Bubble2D/Roboarm/3D-Models/3mf-Files/Handteile/Fingerteile/Connector Typ 1/Finger-FingerConnector-Binder_groß.3mf

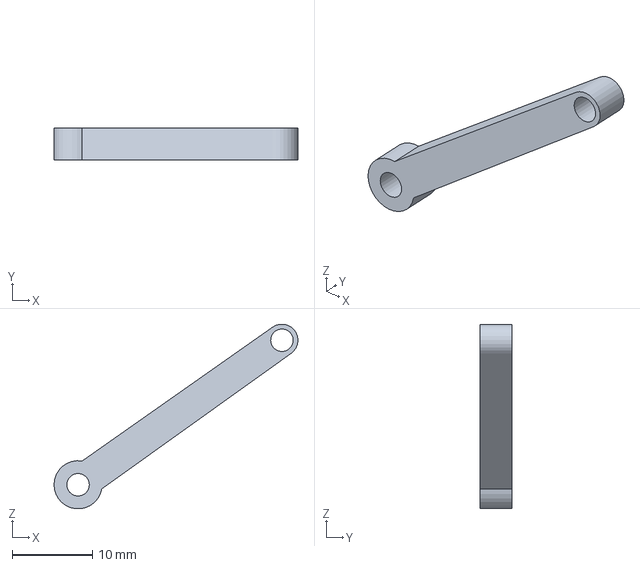
[picture p16: CAD file, 2025-01-12]
3D-Models/3mf-Files/Handteile/Fingerteile/Connector Typ 1/Finger-FingerConnector-Binder_groß.3mf
30.4 x 4.00 x 23.0 mm
