Bubble2D/Roboarm/3D-Models/3mf-Files/Handteile/Fingerteile/Connector Typ 2/Finger-FingerConnector-Binder_klein.3mf

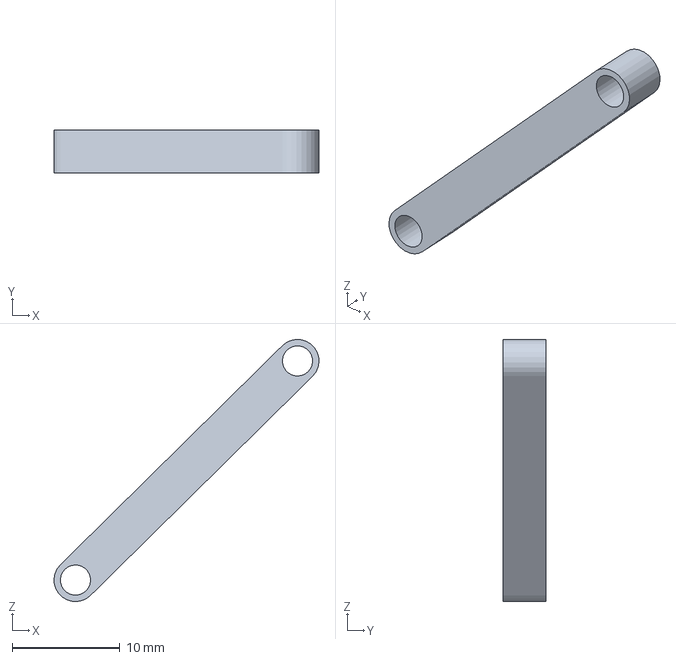
[picture p17: CAD file, 2025-01-12]
3D-Models/3mf-Files/Handteile/Fingerteile/Connector Typ 2/Finger-FingerConnector-Binder_klein.3mf
24.6 x 4.00 x 24.4 mm
