Bubble2D/Roboarm/3D-Models/3mf-Files/Handteile/Fingerteile/Finger-komplett.3mf

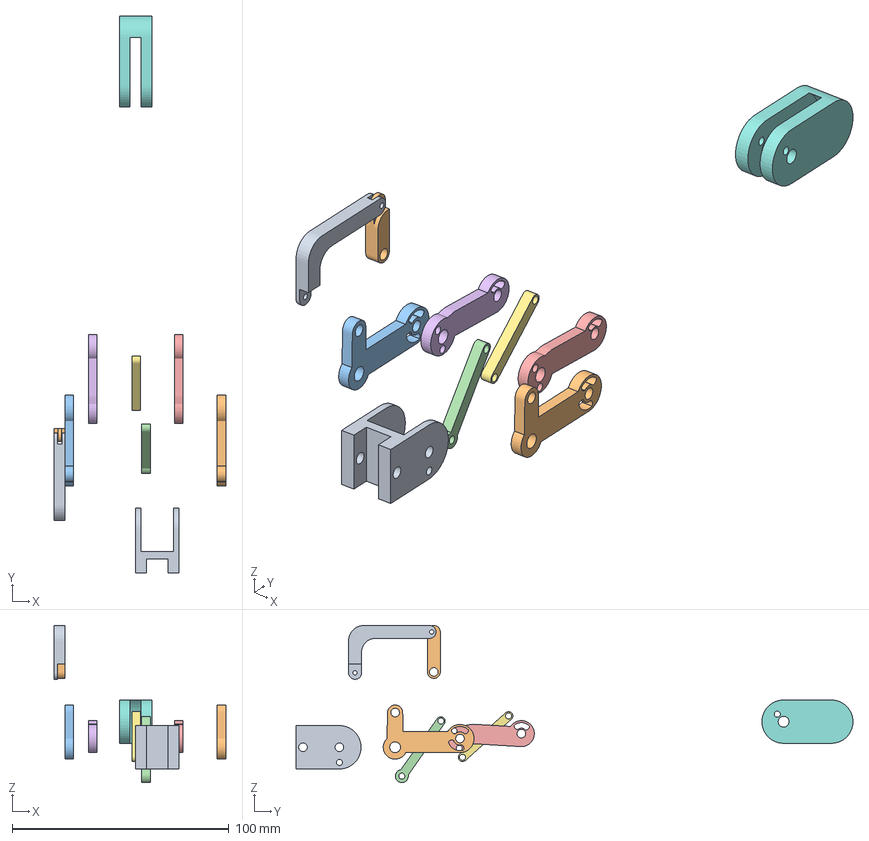
[picture p18: CAD file, 2025-02-24]
3D-Models/3mf-Files/Handteile/Fingerteile/Finger-komplett.3mf
79.1 x 256.8 x 72.5 mm
