Bubble2D/Roboarm/3D-Models/3mf-Files/Handteile/Fingerteile/ServoPins/ServoAufsatz-Körper-Servo-lang.3mf

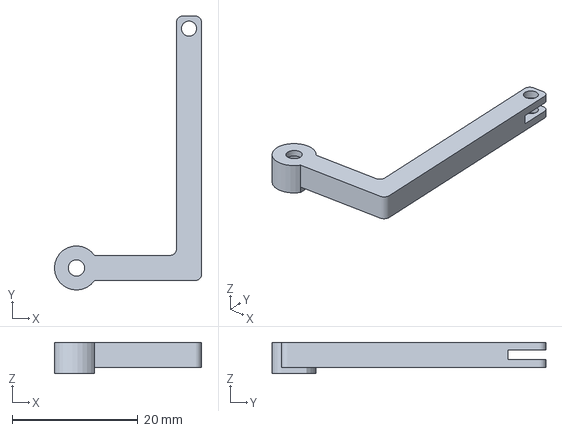
[picture p19: CAD file, 2025-03-01]
3D-Models/3mf-Files/Handteile/Fingerteile/ServoPins/ServoAufsatz-Körper-Servo-lang.3mf
23.4 x 43.5 x 5.00 mm
