Bubble2D/Roboarm/3D-Models/3mf-Files/Handteile/Handgelenk.3mf

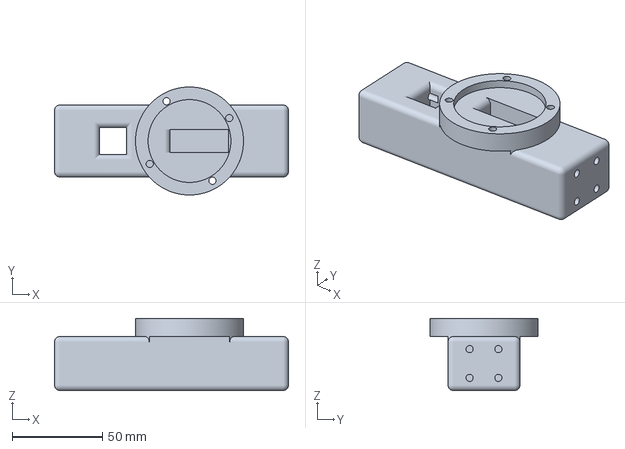
[picture p20: CAD file, 2025-02-24]
3D-Models/3mf-Files/Handteile/Handgelenk.3mf
130.0 x 60.0 x 40.0 mm
