Bubble2D/Roboarm/3D-Models/3mf-Files/Handteile/KugelLager/KugelLager2-Innenlager.3mf

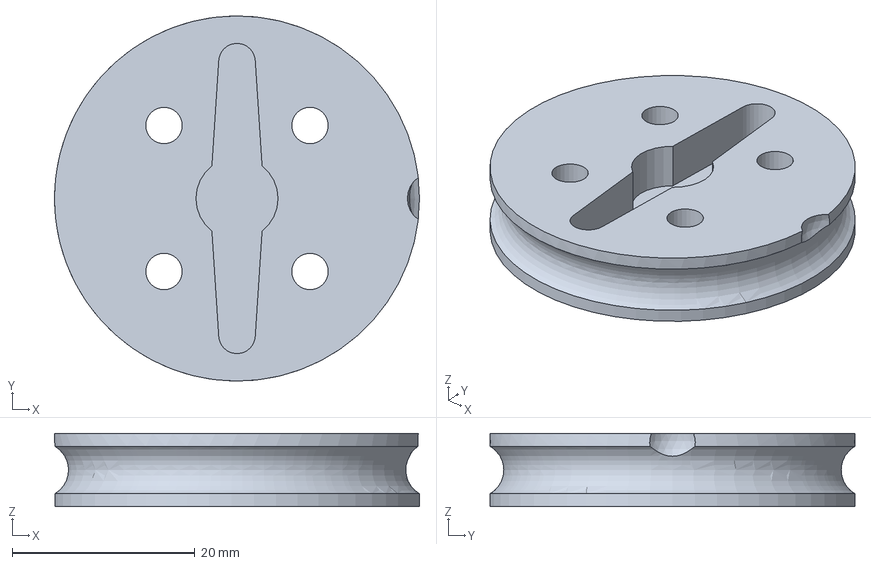
[picture p21: CAD file, 2025-01-13]
3D-Models/3mf-Files/Handteile/KugelLager/KugelLager2-Innenlager.3mf
40.0 x 40.0 x 8.00 mm
