Bubble2D/Roboarm/3D-Models/Hand/Servo/Servo.FCStd

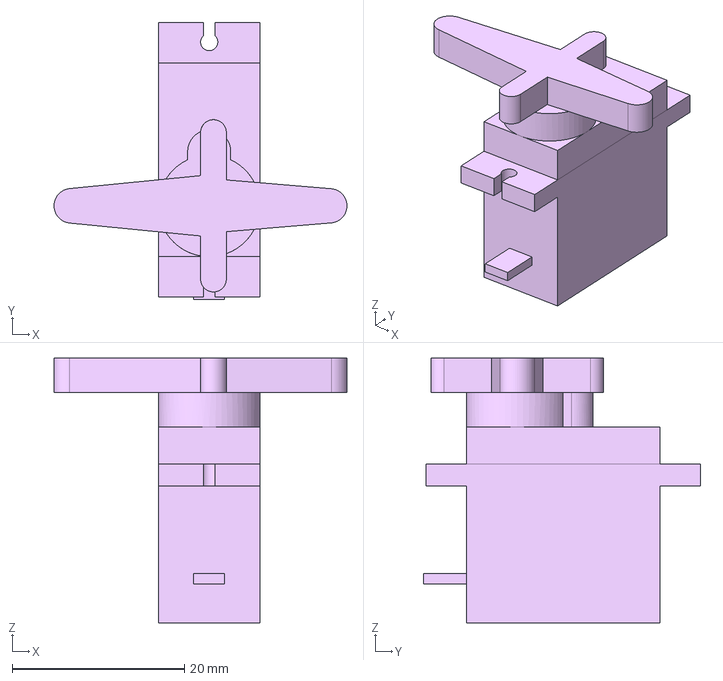
[picture p22: CAD file, 2025-01-08]
3D-Models/Hand/Servo/Servo.FCStd
34.0 x 32.2 x 30.7 mm
