Bubble2D/Roboarm/3D-Models/3mf-Files/Finger und Handgelenk.3mf

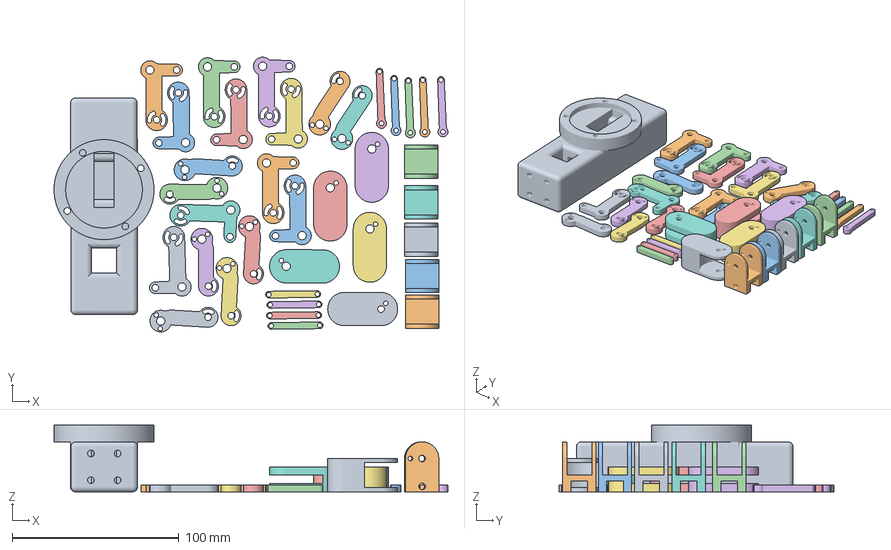
[picture p23: CAD file, 2025-01-13]
3D-Models/3mf-Files/Finger und Handgelenk.3mf
236.3 x 164.8 x 40.0 mm
Handgelenk
Finger-FingerConnector_groß x 10
Finger-FingerConnector_klein x 8
Finger-FingerConnector-Binder_klein x 4
Finger-FingerFingerbasis x 5
Finger-FingerFingerkuppe x 4
Finger-DaumenDaumenkuppe
Finger-FingerConnector-Binder_groß x 5
