Bubble2D/Roboarm/3D-Models/3mf-Files/Handteile/Fingerteile/Connector Typ 2/Finger-FingerConnector_klein.3mf

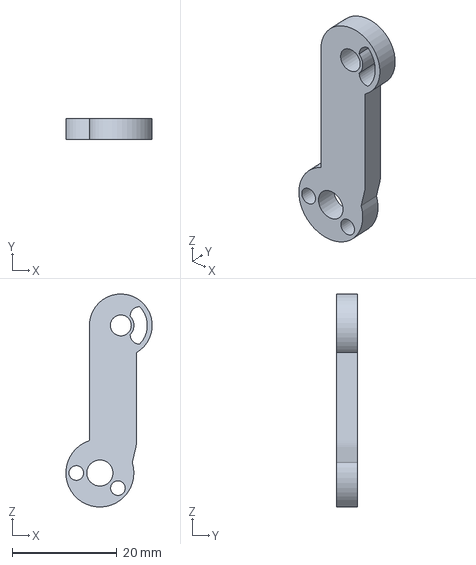
[picture p24: CAD file, 2025-01-12]
3D-Models/3mf-Files/Handteile/Fingerteile/Connector Typ 2/Finger-FingerConnector_klein.3mf
16.5 x 4.00 x 40.7 mm
