Bubble2D/Roboarm/3D-Models/3mf-Files/Handteile/Fingerteile/Finger-DaumenDaumenkuppe.3mf

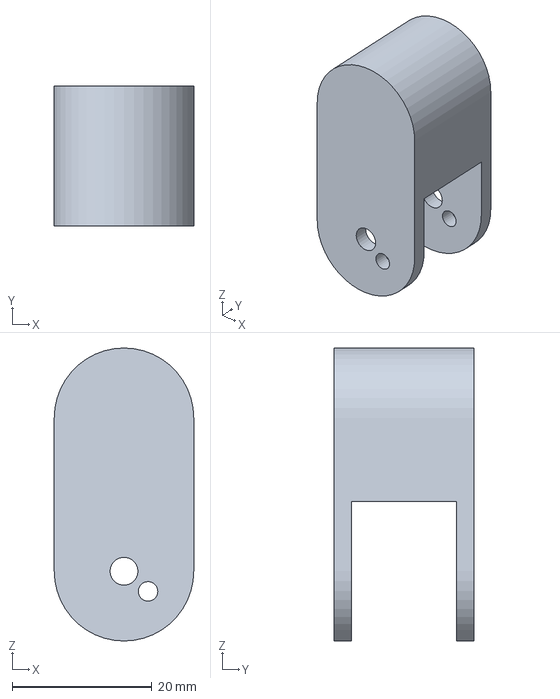
[picture p25: CAD file, 2025-01-13]
3D-Models/3mf-Files/Handteile/Fingerteile/Finger-DaumenDaumenkuppe.3mf
20.0 x 20.0 x 42.0 mm
