Bubble2D/Roboarm/3D-Models/3mf-Files/Handteile/Gelenkthalterung.3mf

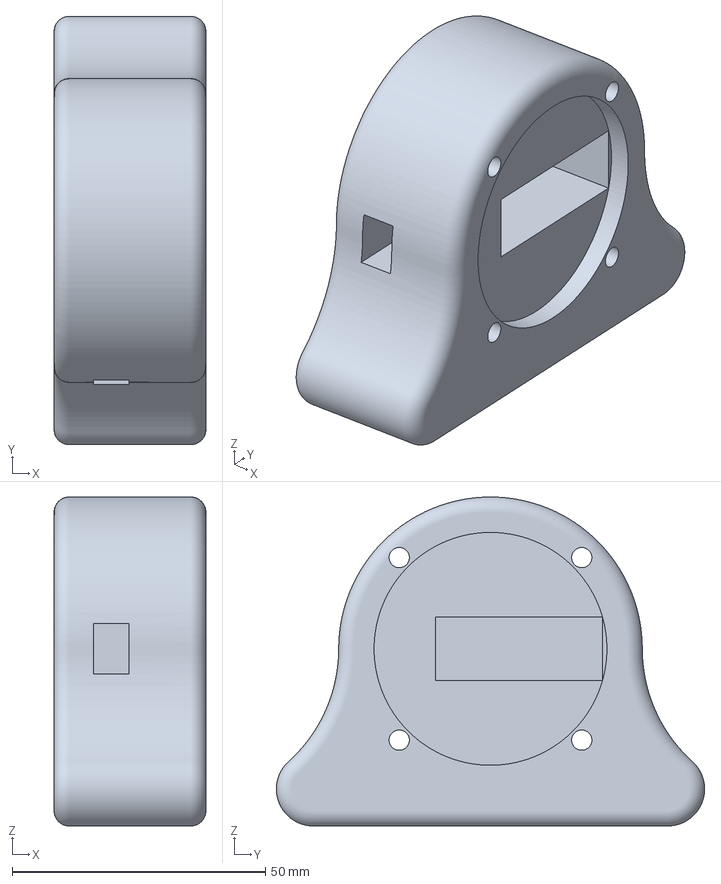
[picture p26: CAD file, 2025-01-16]
3D-Models/3mf-Files/Handteile/Gelenkthalterung.3mf
30.0 x 84.6 x 65.0 mm
