Bubble2D/Roboarm/3D-Models/Hand/Servo/ServoZahnrad.FCStd

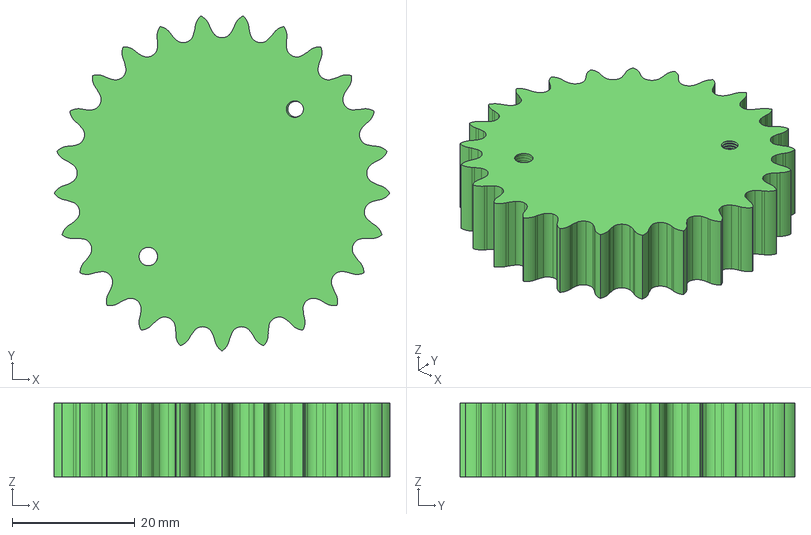
[picture p27: CAD file, 2025-01-08]
3D-Models/Hand/Servo/ServoZahnrad.FCStd
54.7 x 54.6 x 12.0 mm
