Bubble2D/Roboarm/3D-Models/3mf-Files/Handteile/Fingerteile/Finger-FingerFingerkuppe.3mf

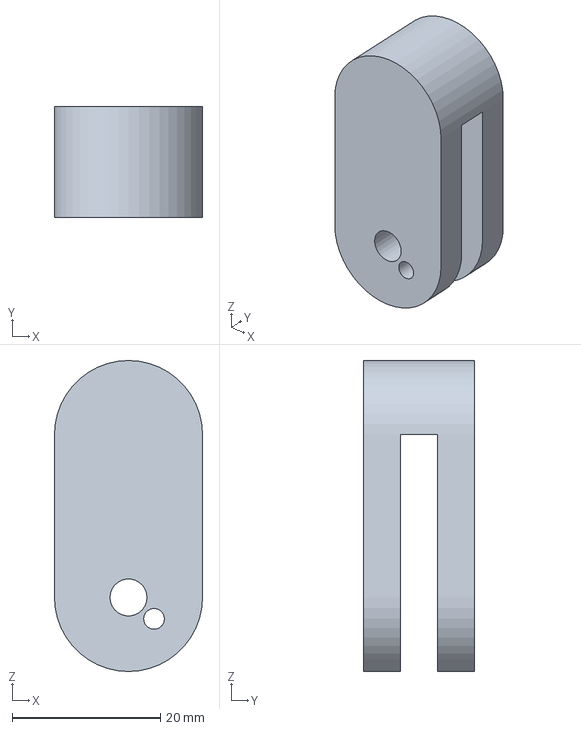
[picture p28: CAD file, 2025-01-12]
3D-Models/3mf-Files/Handteile/Fingerteile/Finger-FingerFingerkuppe.3mf
20.0 x 15.0 x 42.0 mm
