Bubble2D/Roboarm/3D-Models/3mf-Files/Handteile/Fingerteile/ServoPins/ServoAufsatz-Körper-Finger-lang.3mf

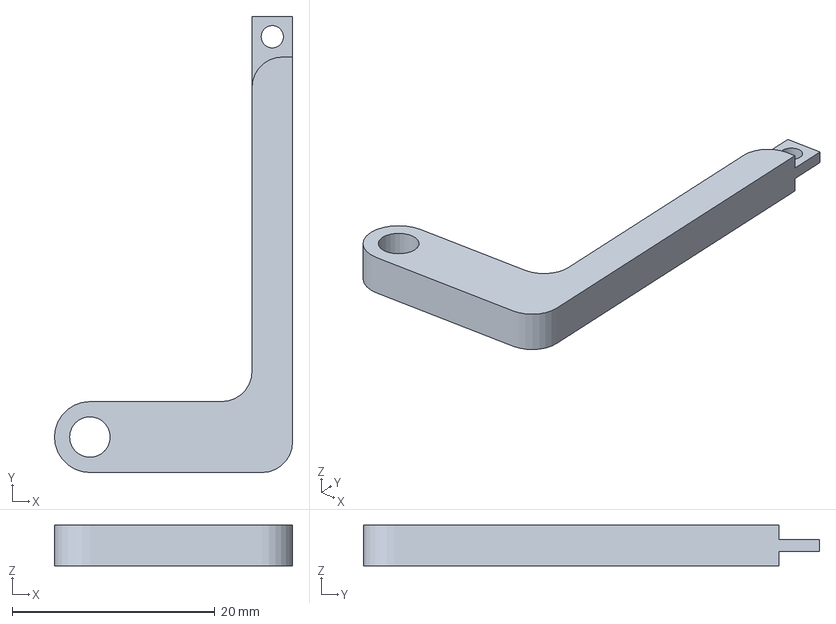
[picture p29: CAD file, 2025-03-01]
3D-Models/3mf-Files/Handteile/Fingerteile/ServoPins/ServoAufsatz-Körper-Finger-lang.3mf
23.5 x 45.0 x 4.00 mm
