Bubble2D/Roboarm/3D-Models/Hand/Servo/SockelZahnrad.FCStd

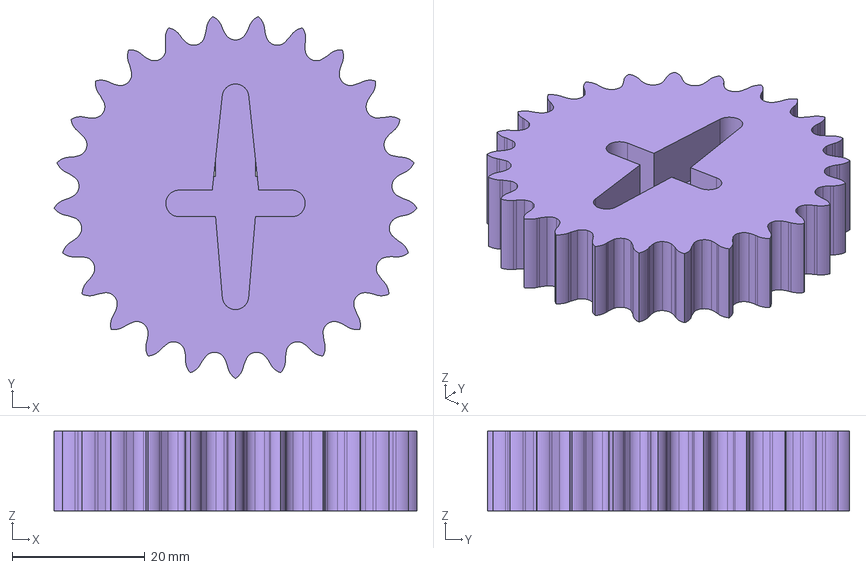
[picture p30: CAD file, 2025-01-05]
3D-Models/Hand/Servo/SockelZahnrad.FCStd
54.7 x 54.6 x 12.0 mm
