Bubble2D/Roboarm/3D-Models/3mf-Files/Handteile/Fingerteile/ServoPins/Finger-FingerServoPin_Servo.3mf

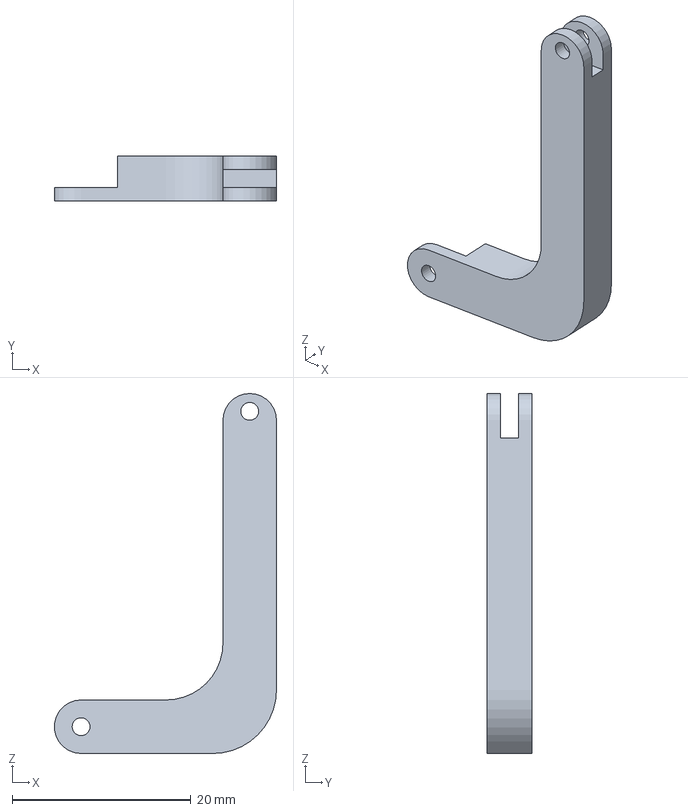
[picture p31: CAD file, 2025-02-24]
3D-Models/3mf-Files/Handteile/Fingerteile/ServoPins/Finger-FingerServoPin_Servo.3mf
24.9 x 5.00 x 40.3 mm
