Bubble2D/Roboarm/3D-Models/3mf-Files/Handteile/Fingerteile/ServoPins/ServoAufsatz-Körper.3mf

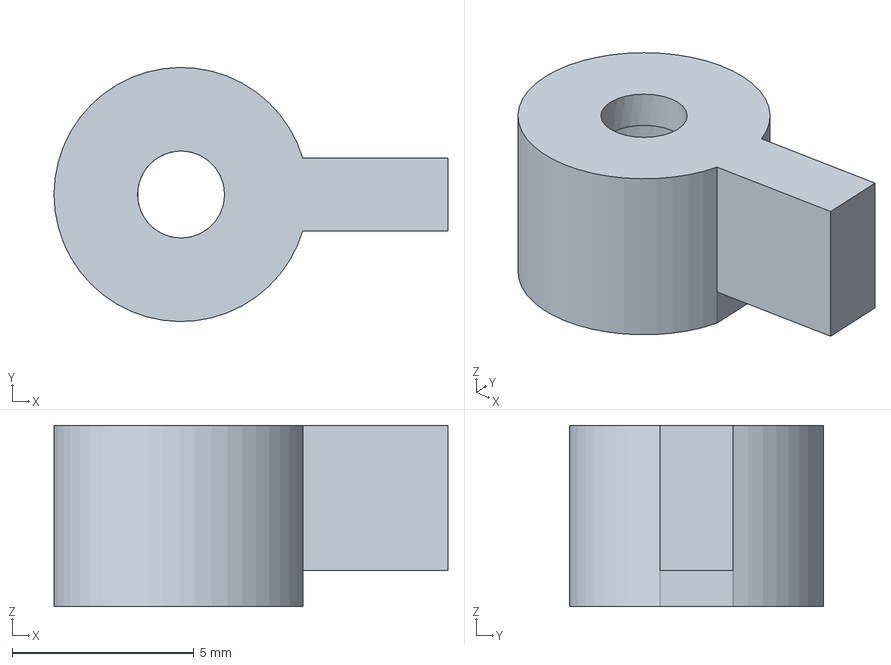
[picture p32: CAD file, 2025-02-24]
3D-Models/3mf-Files/Handteile/Fingerteile/ServoPins/ServoAufsatz-Körper.3mf
10.9 x 7.00 x 5.00 mm
