Bubble2D/Roboarm/3D-Models/3mf-Files/Handteile/Fingerteile/ServoPins/ServoAufsatz-Körper-Finger.3mf

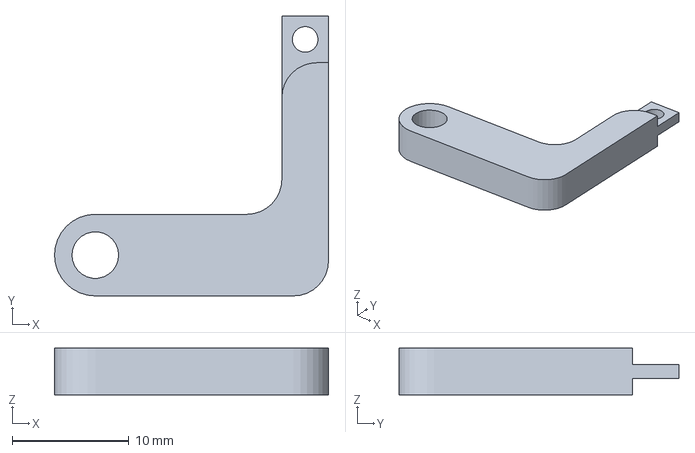
[picture p33: CAD file, 2025-02-24]
3D-Models/3mf-Files/Handteile/Fingerteile/ServoPins/ServoAufsatz-Körper-Finger.3mf
23.5 x 24.0 x 4.00 mm
