Bubble2D/Roboarm/3D-Models/3mf-Files/Handteile/Fingerteile/ServoPins/Finger-FingerServoPin_Finger.3mf

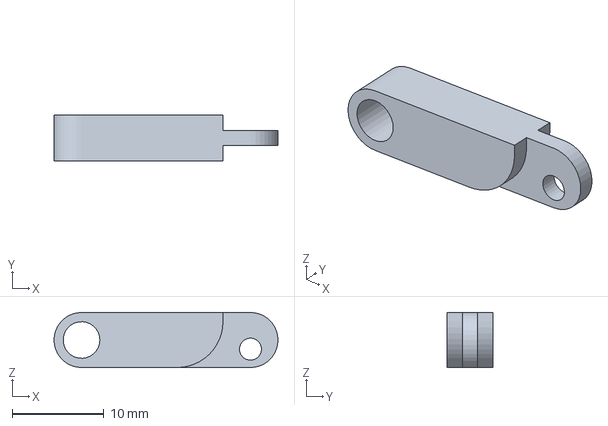
[picture p34: CAD file, 2025-02-24]
3D-Models/3mf-Files/Handteile/Fingerteile/ServoPins/Finger-FingerServoPin_Finger.3mf
24.4 x 5.00 x 6.00 mm
