Bubble2D/Roboarm/3D-Models/3mf-Files/Handteile/Fingerteile/ServoPins/Finger-FingerServoPin.3mf

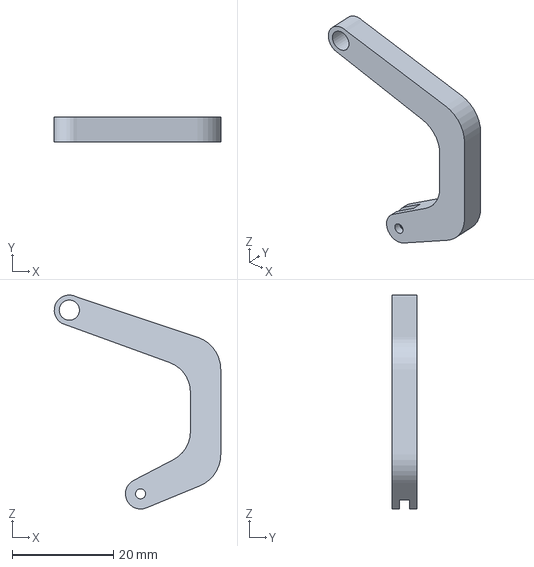
[picture p35: CAD file, 2025-01-12]
3D-Models/3mf-Files/Handteile/Fingerteile/ServoPins/Finger-FingerServoPin.3mf
32.9 x 5.00 x 42.3 mm
